CarlosGS/PrintrCamBot/Media/IMG_0274.JPG

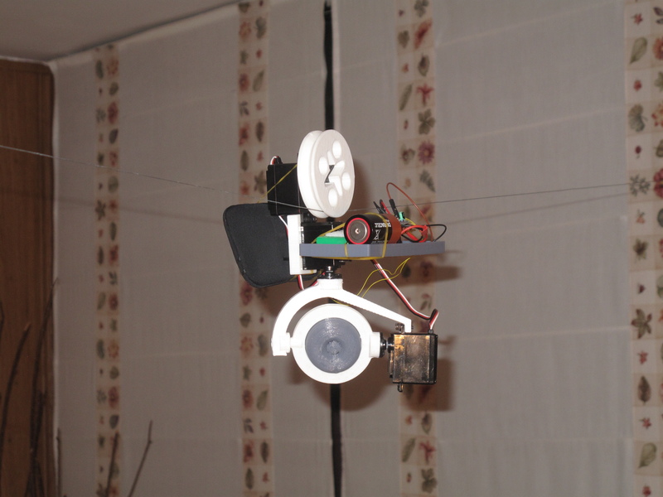
Media/IMG_0274.JPG
