CarlosGS/PrintrCamBot/Media/IMG_0276.JPG

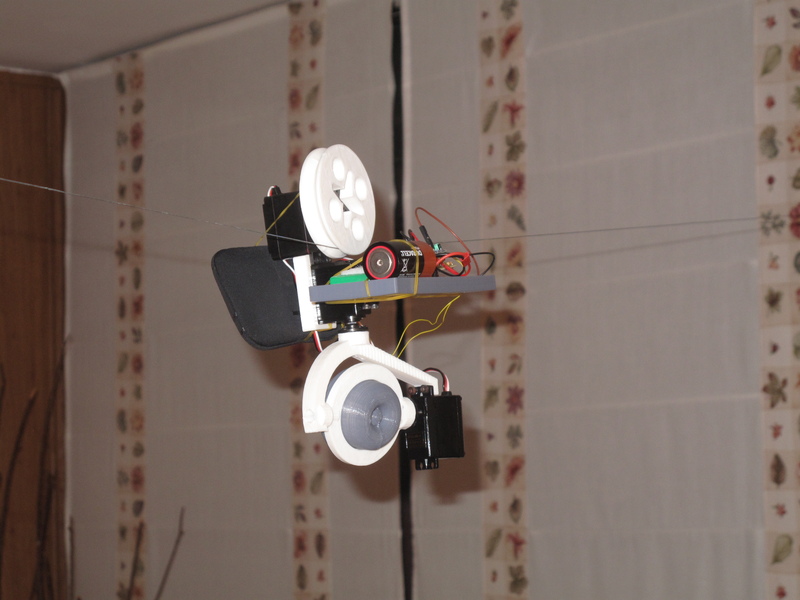
Media/IMG_0276.JPG
