CarlosGS/PrintrCamBot/Media/IMG_0277.JPG

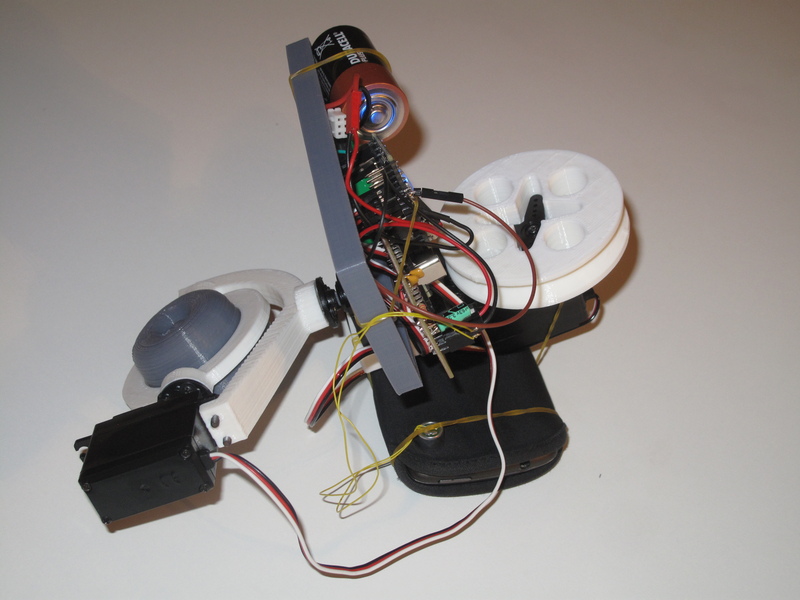
Media/IMG_0277.JPG
