CarlosGS/PrintrCamBot/Media/IMG_0278.JPG

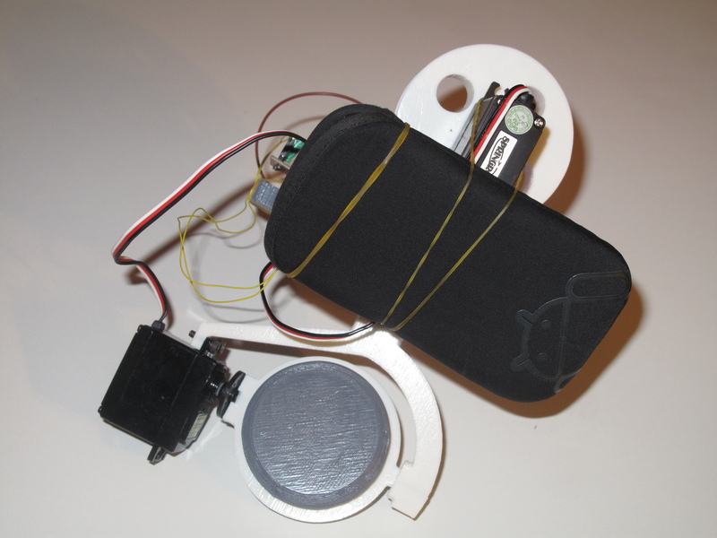
Media/IMG_0278.JPG
