CarlosGS/PrintrCamBot/Media/IMG_0279.JPG

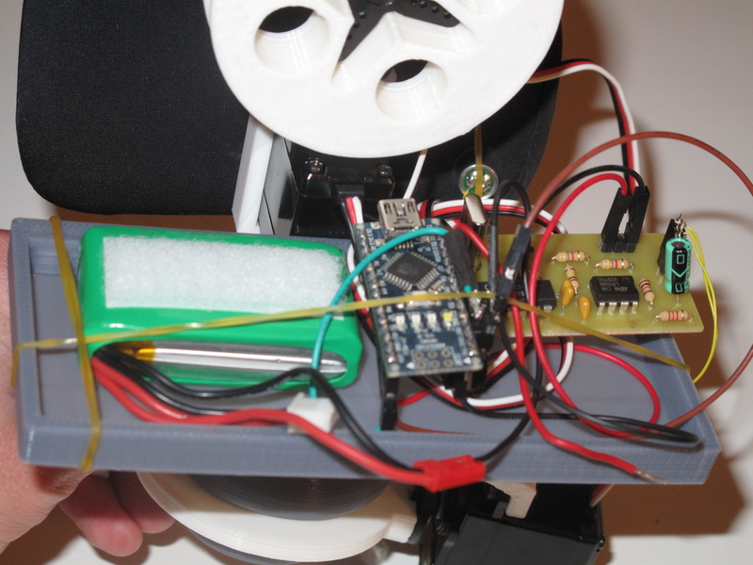
Media/IMG_0279.JPG
