CarlosGS/PrintrCamBot/Media/IMG_0280.JPG

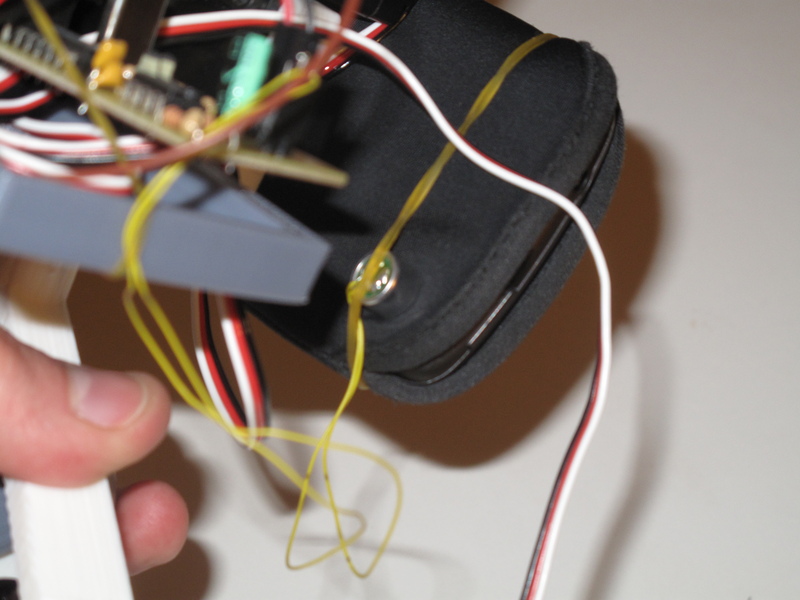
Media/IMG_0280.JPG
