CarlosGS/PrintrCamBot/Media/IMG_0281.JPG

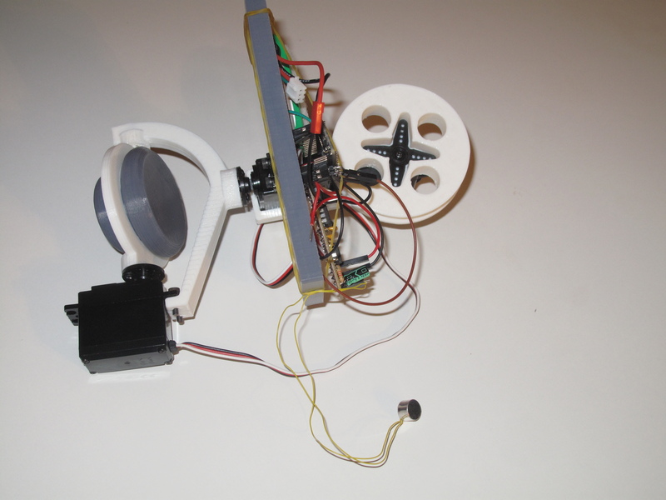
Media/IMG_0281.JPG
