CarlosGS/PrintrCamBot/Electronics/DTMF-Decoder/ManufactureProcess/2013-06-04 21.43.28.jpg

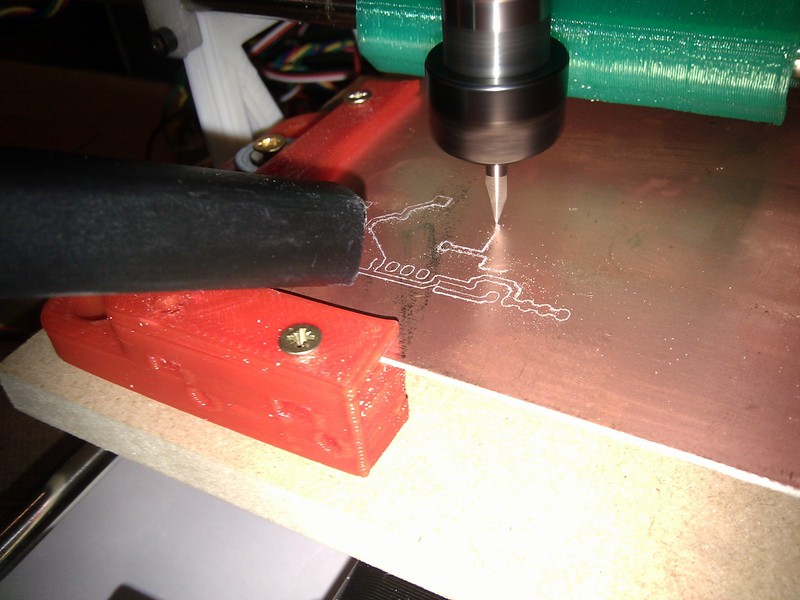
Electronics/DTMF-Decoder/ManufactureProcess/2013-06-04 21.43.28.jpg
