CarlosGS/PrintrCamBot/Electronics/DTMF-Decoder/ManufactureProcess/2013-06-04 21.46.15.jpg

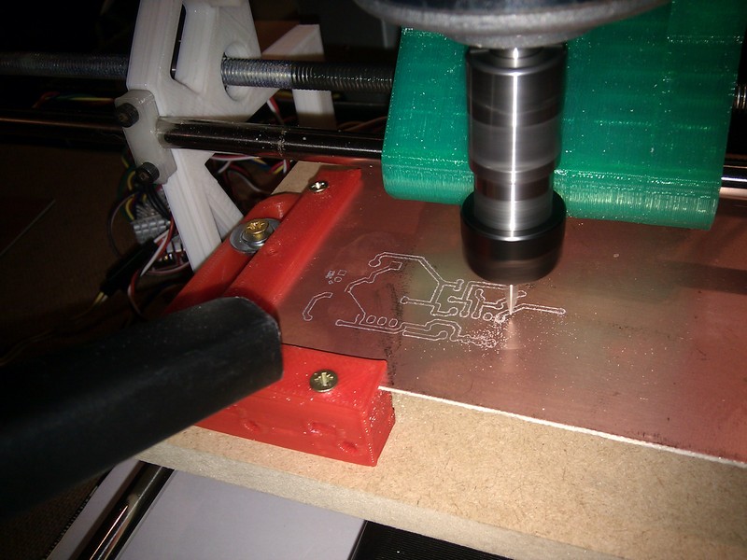
Electronics/DTMF-Decoder/ManufactureProcess/2013-06-04 21.46.15.jpg
