CarlosGS/PrintrCamBot/Electronics/DTMF-Decoder/ManufactureProcess/2013-06-04 21.49.59.jpg

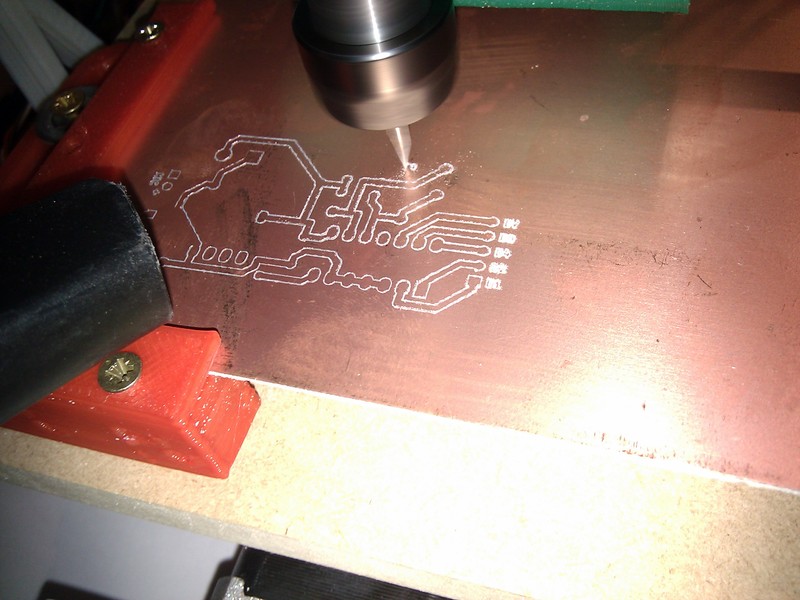
Electronics/DTMF-Decoder/ManufactureProcess/2013-06-04 21.49.59.jpg
