CarlosGS/PrintrCamBot/Electronics/DTMF-Decoder/ManufactureProcess/2013-06-04 21.54.49.jpg

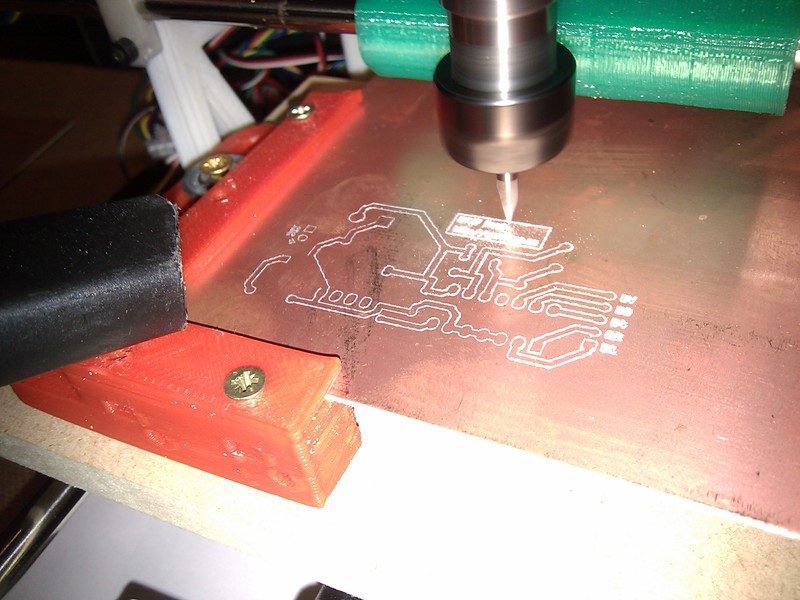
Electronics/DTMF-Decoder/ManufactureProcess/2013-06-04 21.54.49.jpg
