CarlosGS/PrintrCamBot/Electronics/DTMF-Decoder/ManufactureProcess/2013-06-05 16.21.47.jpg

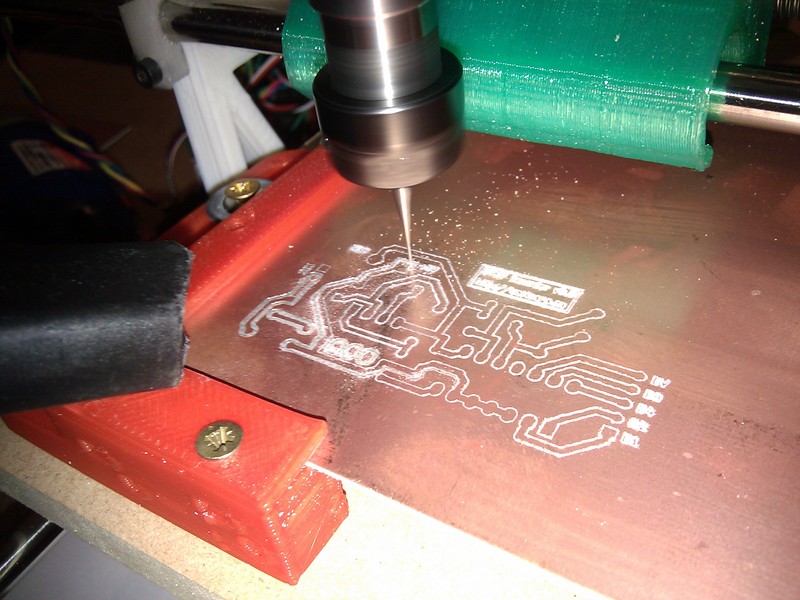
Electronics/DTMF-Decoder/ManufactureProcess/2013-06-05 16.21.47.jpg
