CarlosGS/PrintrCamBot/Electronics/DTMF-Decoder/ManufactureProcess/2013-06-05 16.25.16.jpg

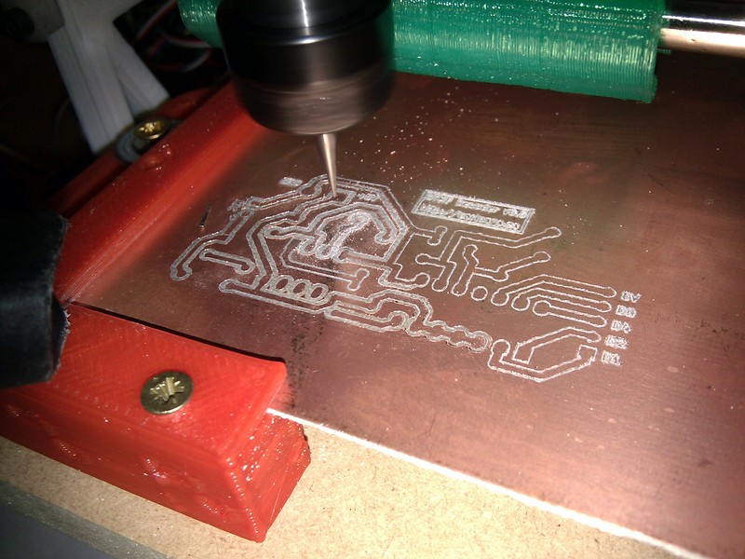
Electronics/DTMF-Decoder/ManufactureProcess/2013-06-05 16.25.16.jpg
