CarlosGS/PrintrCamBot/Electronics/DTMF-Decoder/ManufactureProcess/2013-06-05 16.53.43.jpg

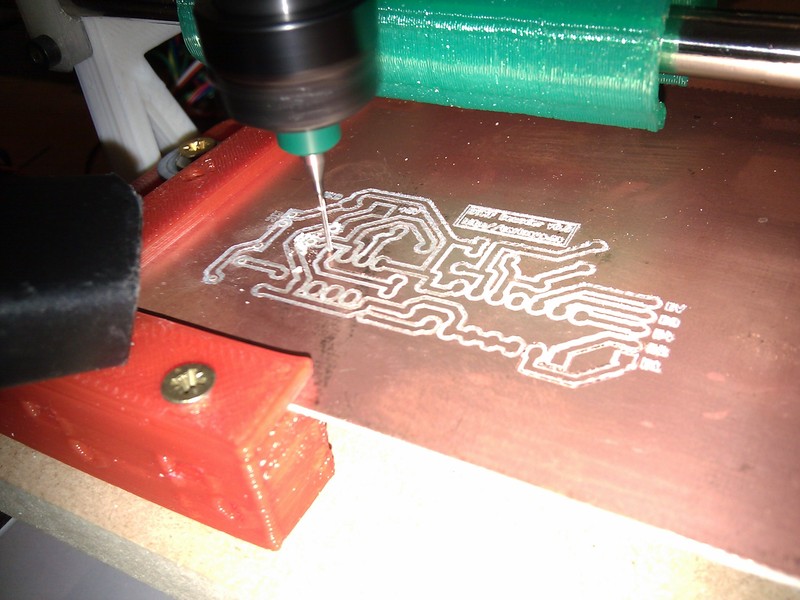
Electronics/DTMF-Decoder/ManufactureProcess/2013-06-05 16.53.43.jpg
