CarlosGS/PrintrCamBot/Electronics/DTMF-Decoder/ManufactureProcess/2013-06-05 16.59.24.jpg

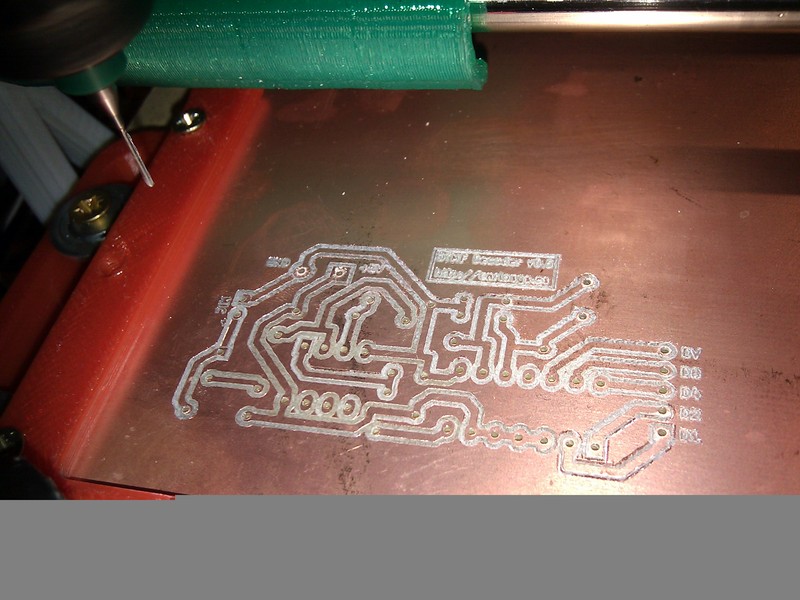
Electronics/DTMF-Decoder/ManufactureProcess/2013-06-05 16.59.24.jpg
