CarlosGS/PrintrCamBot/Electronics/DTMF-Decoder/ManufactureProcess/2013-06-05 17.28.39.jpg

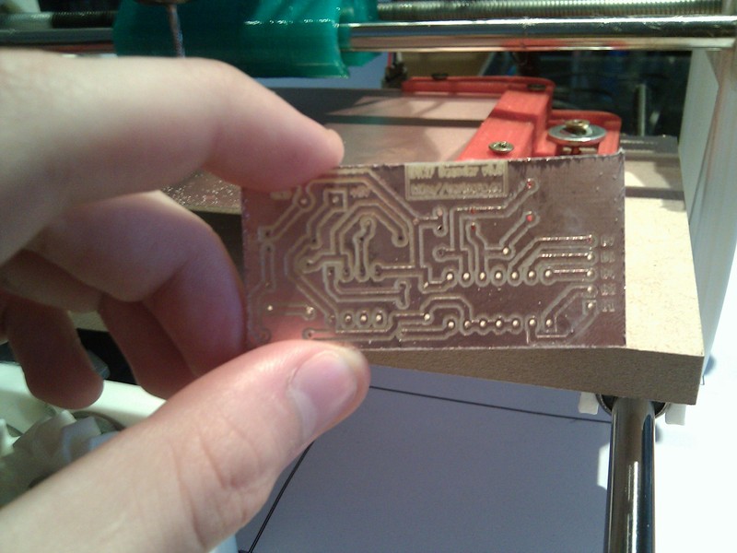
Electronics/DTMF-Decoder/ManufactureProcess/2013-06-05 17.28.39.jpg
