CarlosGS/PrintrCamBot/Electronics/DTMF-Decoder/ManufactureProcess/2013-06-05 17.29.07.jpg

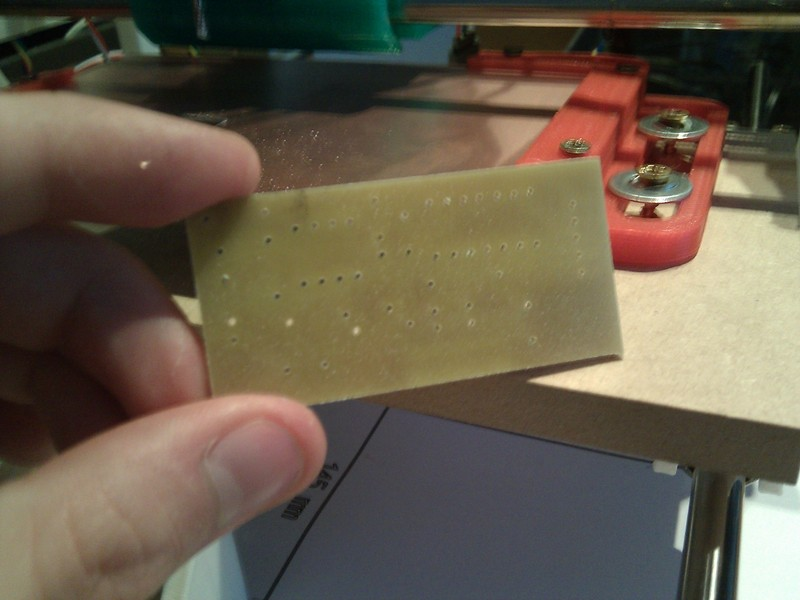
Electronics/DTMF-Decoder/ManufactureProcess/2013-06-05 17.29.07.jpg
