CarlosGS/PrintrCamBot/Electronics/DTMF-Decoder/ManufactureProcess/2013-06-05 17.34.33.jpg

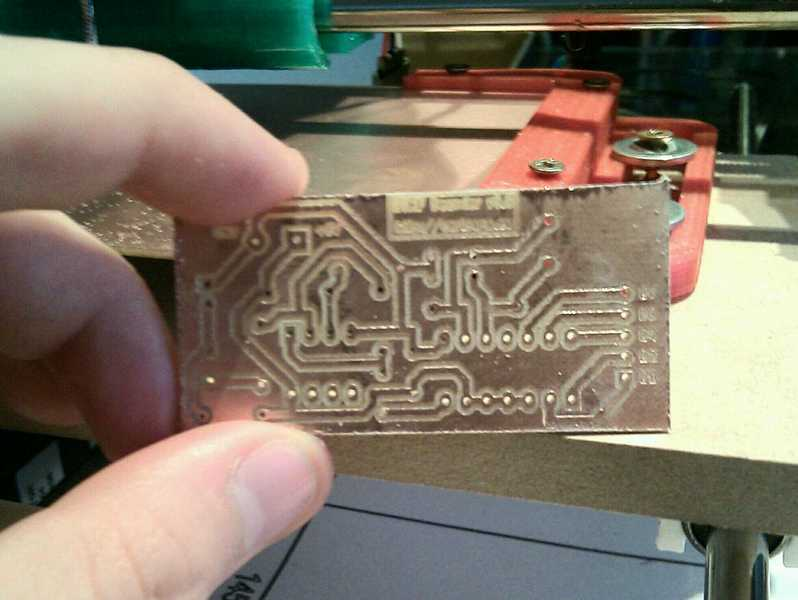
Electronics/DTMF-Decoder/ManufactureProcess/2013-06-05 17.34.33.jpg
