CarlosGS/PrintrCamBot/Electronics/DTMF-Decoder/ManufactureProcess/2013-06-05 18.31.42.jpg

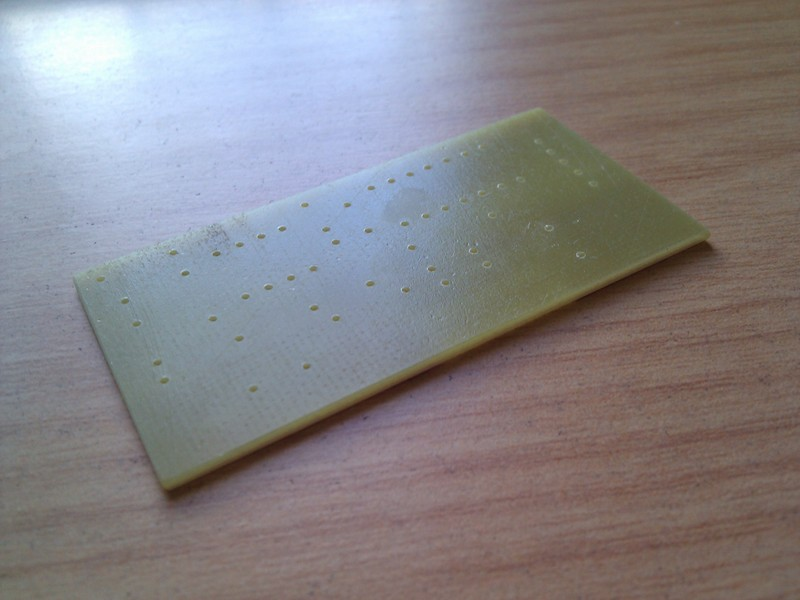
Electronics/DTMF-Decoder/ManufactureProcess/2013-06-05 18.31.42.jpg
