CarlosGS/PrintrCamBot/Electronics/DTMF-Decoder/ManufactureProcess/2013-06-05 19.07.09.jpg

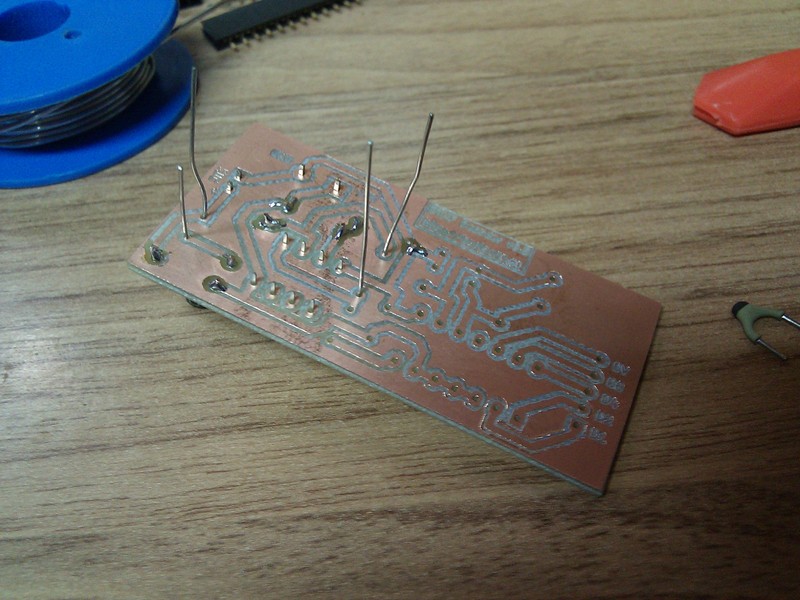
Electronics/DTMF-Decoder/ManufactureProcess/2013-06-05 19.07.09.jpg
