CarlosGS/PrintrCamBot/Electronics/DTMF-Decoder/ManufactureProcess/2013-06-05 19.11.20.jpg

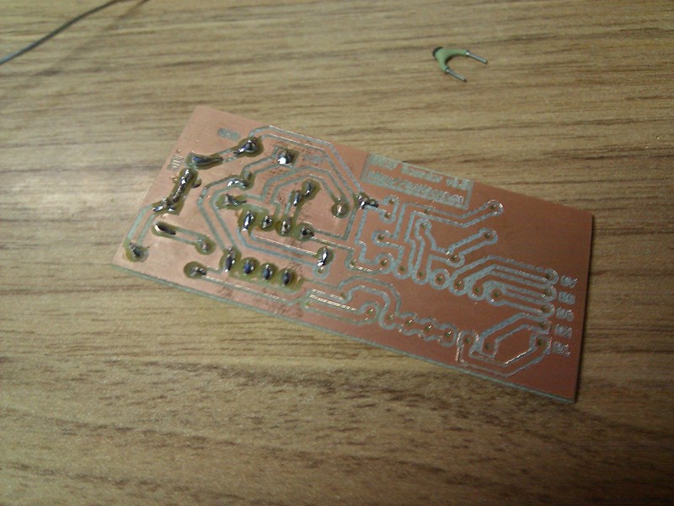
Electronics/DTMF-Decoder/ManufactureProcess/2013-06-05 19.11.20.jpg
