CarlosGS/PrintrCamBot/Electronics/DTMF-Decoder/ManufactureProcess/2013-06-05 19.11.26.jpg

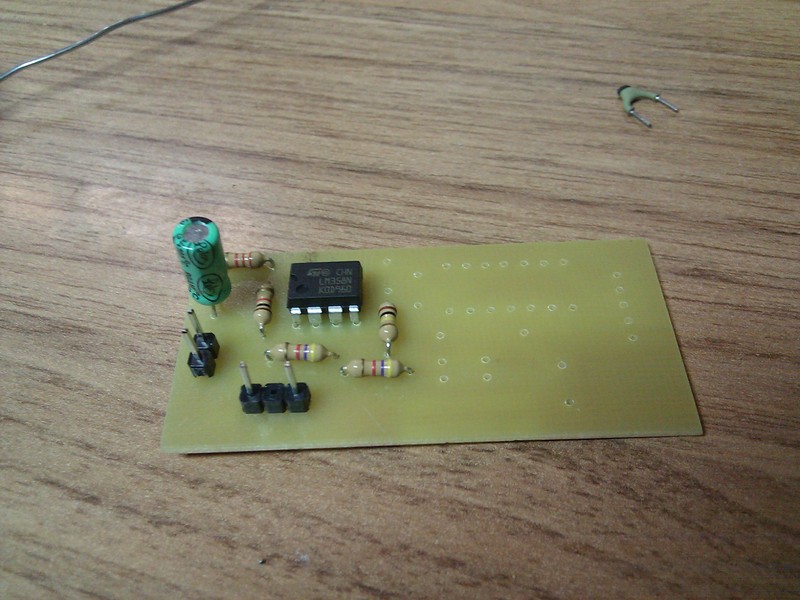
Electronics/DTMF-Decoder/ManufactureProcess/2013-06-05 19.11.26.jpg
