CarlosGS/PrintrCamBot/Electronics/DTMF-Decoder/ManufactureProcess/2013-06-05 19.35.27.jpg

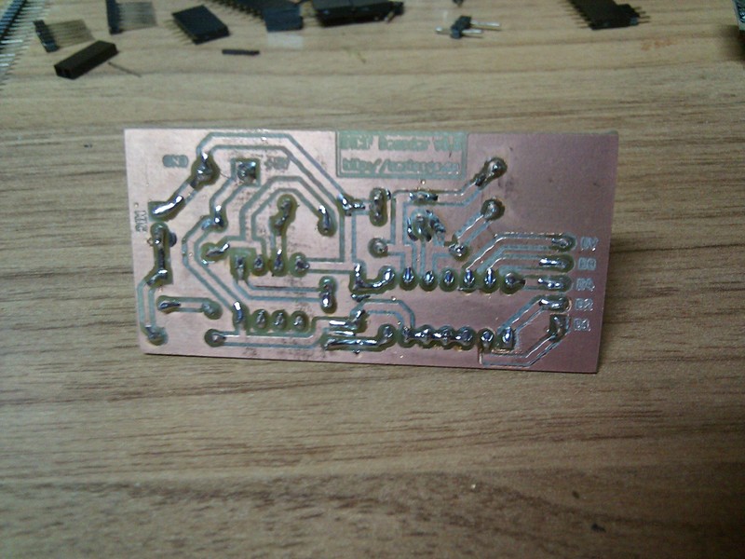
Electronics/DTMF-Decoder/ManufactureProcess/2013-06-05 19.35.27.jpg
